lokuciejewski/mc68k_unicorn/software/firmware/hal/inc/serial.h

#pragma once

#include "../../system/result_codes.h"
#include <stdbool.h>
#include <stddef.h>
#include <stdint.h>

typedef enum {
  Serial_A,
  Serial_B,
} Serial_Instance_e;

// Assuming Baudrate set 1 (ACR[7] = 0) and 1.8432Mhz clock (twice as slow)
typedef enum {
  Serial_Baudrate_300 = 0b01010101,
  Serial_Baudrate_19200 = 0b11001100,
} Serial_Baudrate_e;

typedef enum {
  Serial_8n = 0b10011,
  Serial_7e = 0b00010,
} Serial_Bitconf_e;

typedef enum {
  Serial_StopBits1 = 0b0111,
  Serial_StopBits2 = 0b1111,
} Serial_StopBits_e;

typedef struct {
  Serial_Instance_e instance;
  Serial_Baudrate_e baudrate;
  Serial_Bitconf_e bit_conf;
  Serial_StopBits_e stop_bits;
  bool rx_rts;
  bool tx_rts;
  bool cts;
} Serial_Settings_t;

/// Init the serial port based on settings parameter
void Serial_Init(const Serial_Settings_t *settings);

/// Serial IRQ
void Serial_RxIrq(const Serial_Instance_e instance);

/// Print a character to a specified serial port
void Serial_Putc(const Serial_Instance_e instance, char c);

/// Get a character from the specified serial port
char Serial_Getc(const Serial_Instance_e instance);

/// Get a character from the specified serial port with a specified timeout.
/// After the timeout, the character returned is set to EOF and the returned
/// result is set to UniRes_Timeout
UnicornResult_e Serial_GetcT(const Serial_Instance_e instance,
                             uint16_t timeout_ms, char *out);

/// Print a null-terminated string to the specified serial port
void Serial_PrintStr(const Serial_Instance_e instance, const char *str);

/// Write `count` bytes to serial from `buf`
size_t Serial_WriteBytes(const Serial_Instance_e instance, const uint8_t *buf,
                       size_t count);

/// Read `count` bytes from serial to `buf`
size_t Serial_ReadBytes(const Serial_Instance_e instance, uint8_t *buf,
                      size_t count);
