lokuciejewski/mc68k_unicorn/software/firmware/hal/inc/duart.h

#pragma once

#include "irq.h"
#include <stdint.h>

#define DUART_BASE 0x110000

#define DUART_MR1A (DUART_BASE + 0x01)
#define DUART_MR2A (DUART_BASE + 0x01)
#define DUART_SRA (DUART_BASE + 0x03)
#define DUART_CSRA (DUART_BASE + 0x03)
#define DUART_CRA (DUART_BASE + 0x05)
#define DUART_MISR (DUART_BASE + 0x05)
#define DUART_RBA (DUART_BASE + 0x07)
#define DUART_TBA (DUART_BASE + 0x07)
#define DUART_IPCR (DUART_BASE + 0x09)
#define DUART_ACR (DUART_BASE + 0x09)
#define DUART_ISR (DUART_BASE + 0x0B)
#define DUART_IMR (DUART_BASE + 0x0B)
#define DUART_CUR (DUART_BASE + 0x0D)
#define DUART_CLR (DUART_BASE + 0x0F)
#define DUART_MR1B (DUART_BASE + 0x11)
#define DUART_MR2B (DUART_BASE + 0x11)
#define DUART_SRB (DUART_BASE + 0x13)
#define DUART_CSRB (DUART_BASE + 0x13)
#define DUART_CRB (DUART_BASE + 0x15)
#define DUART_RBB (DUART_BASE + 0x17)
#define DUART_TBB (DUART_BASE + 0x17)
#define DUART_IVR (DUART_BASE + 0x19)
#define DUART_IP (DUART_BASE + 0x1B)
#define DUART_OPCR (DUART_BASE + 0x1B)
#define DUART_OPR_SET (DUART_BASE + 0x1D)
#define DUART_START_CNT (DUART_BASE + 0x1D)
#define DUART_OPR_RESET (DUART_BASE + 0x1F)
#define DUART_STOP_CNT (DUART_BASE + 0x1F)

void INTERRUPT DUART_Irq(void);
void DUART_EnableIrq(uint8_t mask);
void DUART_DisableIrq(uint8_t mask);
